Lionel-Lim/data-marble-machine/log/pics/partDesign.jpeg

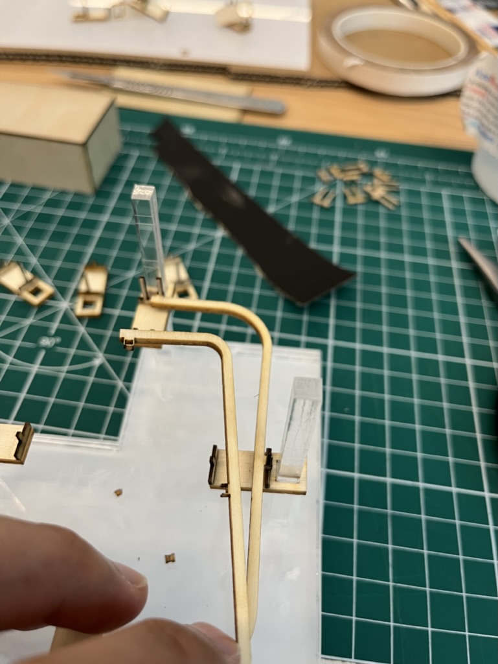
log/pics/partDesign.jpeg
