Lionel-Lim/data-marble-machine/log/pics/wheelWoodMat.jpeg

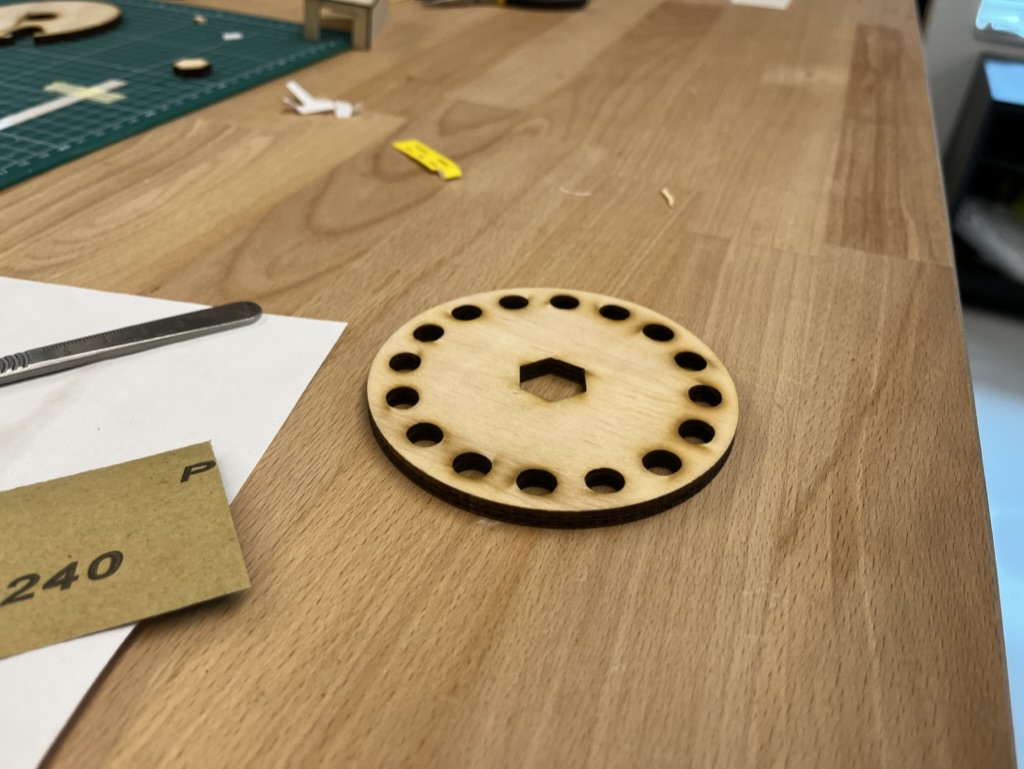
log/pics/wheelWoodMat.jpeg
