Lionel-Lim/data-marble-machine/report/resource/copper lane.png

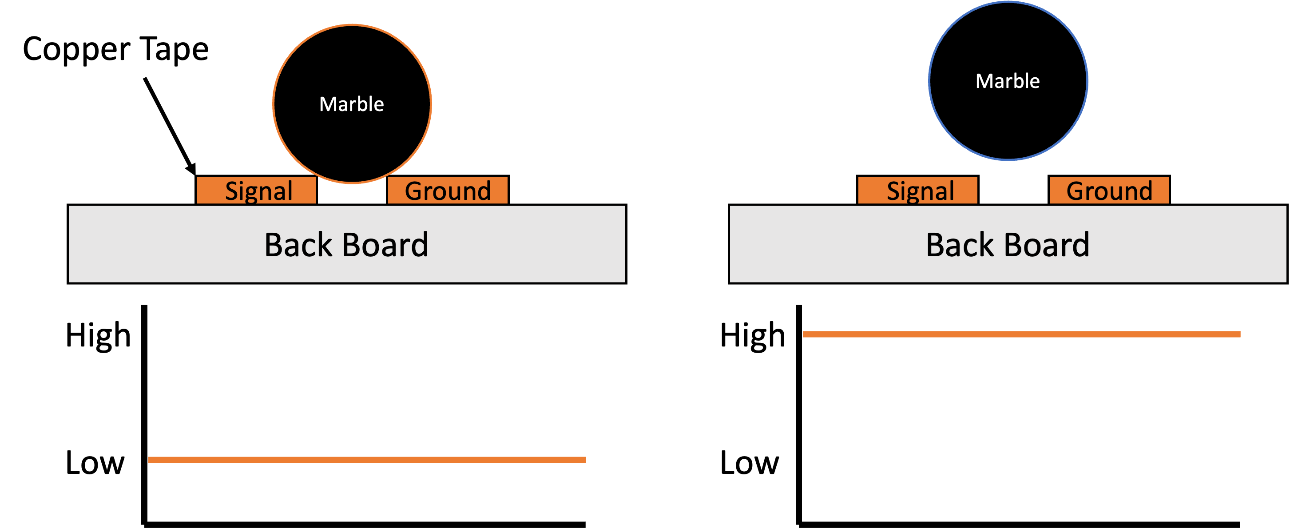
report/resource/copper lane.png
