Lionel-Lim/data-marble-machine/report/resource/device logic.png

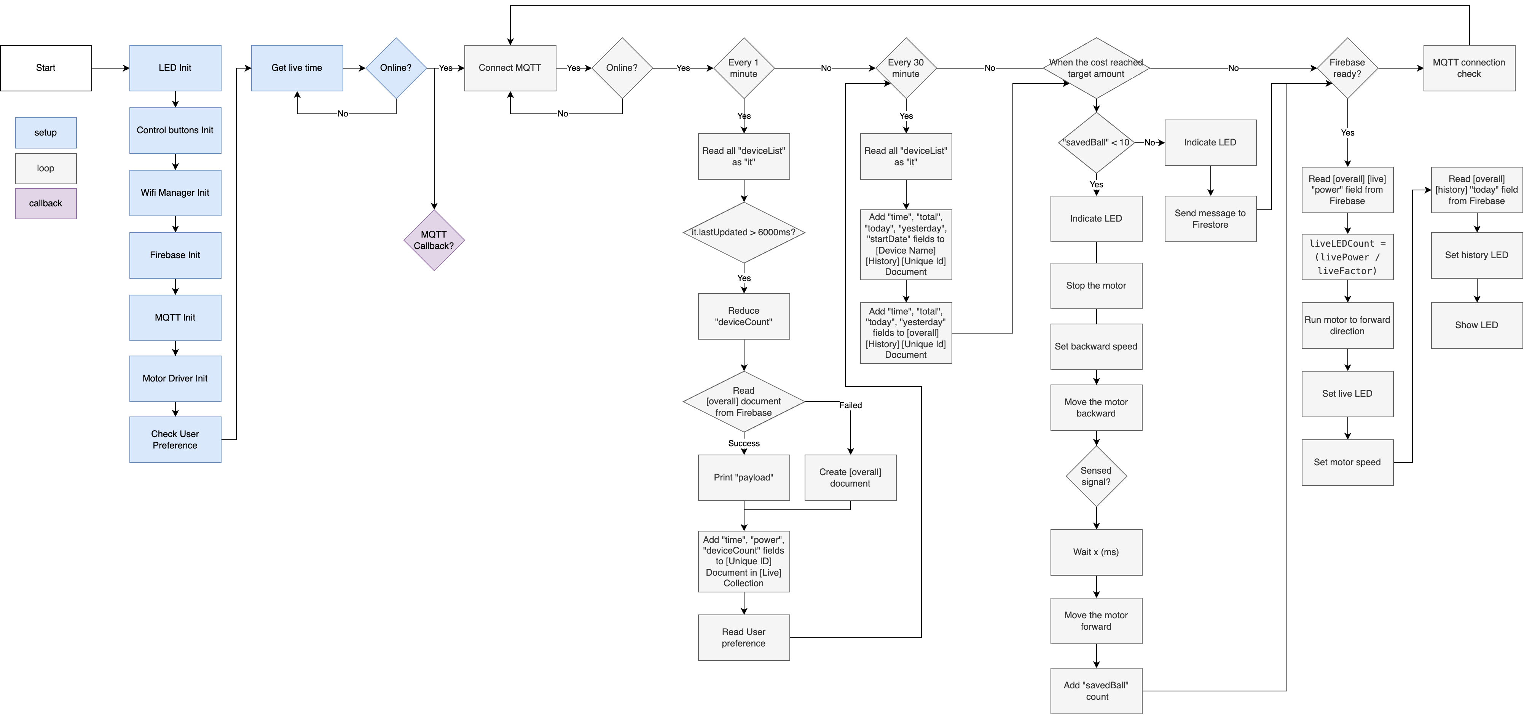
report/resource/device logic.png
