Lionel-Lim/data-marble-machine/report/resource/prototype.png

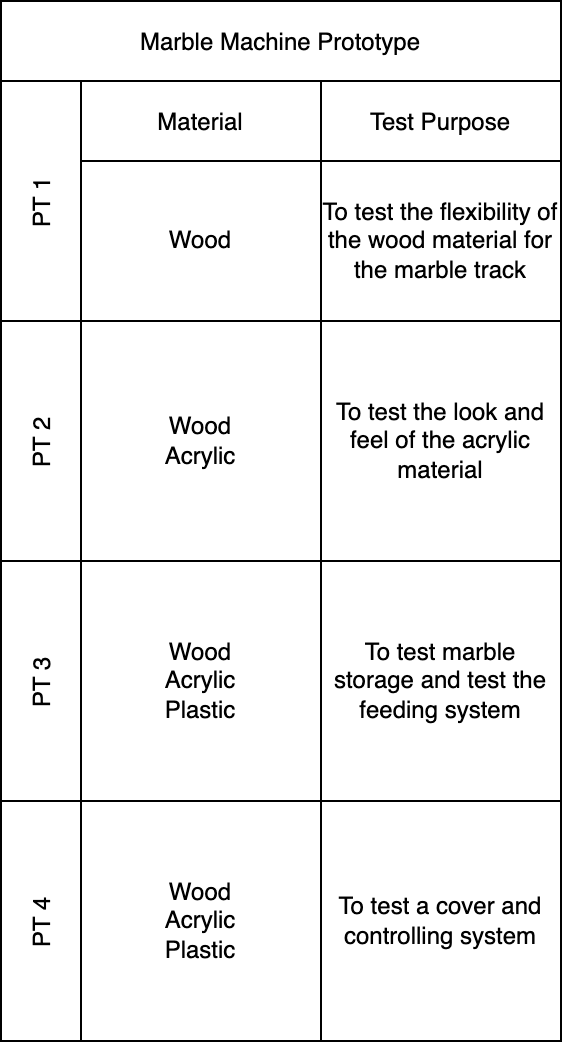
report/resource/prototype.png
