Lionel-Lim/data-marble-machine/report/resource/render.png

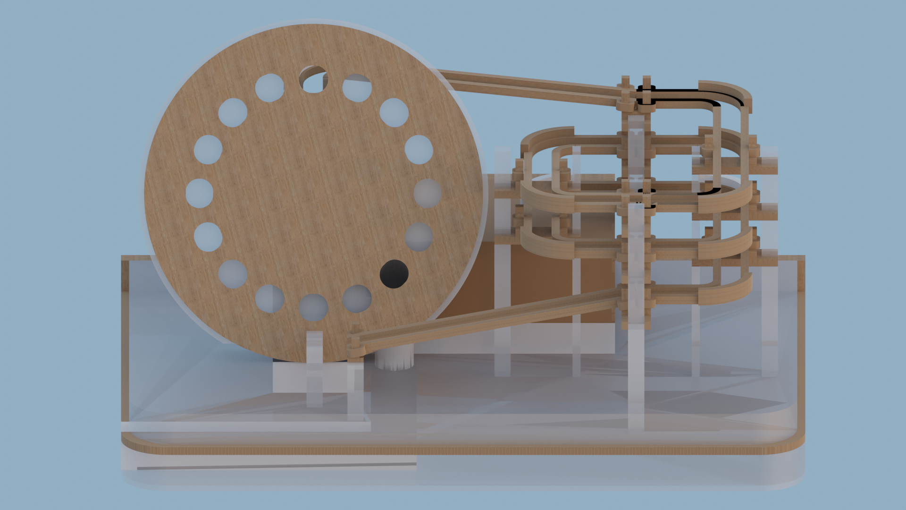
report/resource/render.png
