Lionel-Lim/data-marble-machine/report/resource/track mount.png

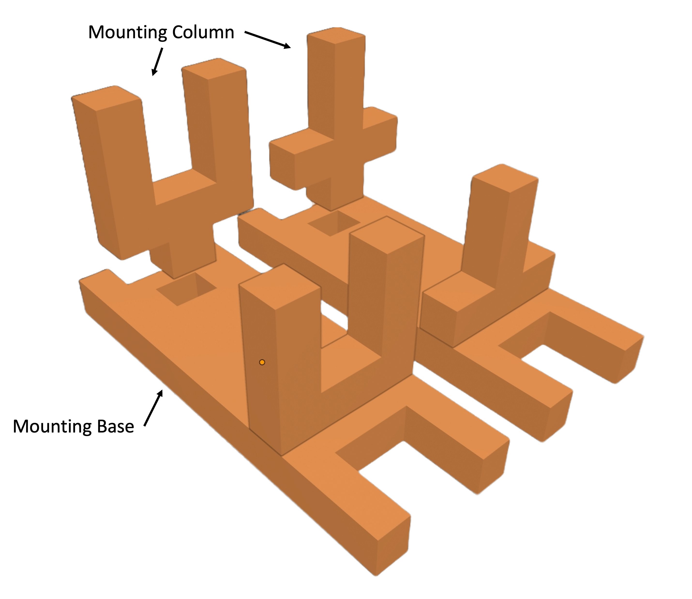
report/resource/track mount.png
