Lionel-Lim/data-marble-machine/models/work in progress/drawings/rev7_NewType/ref_Base.dxf

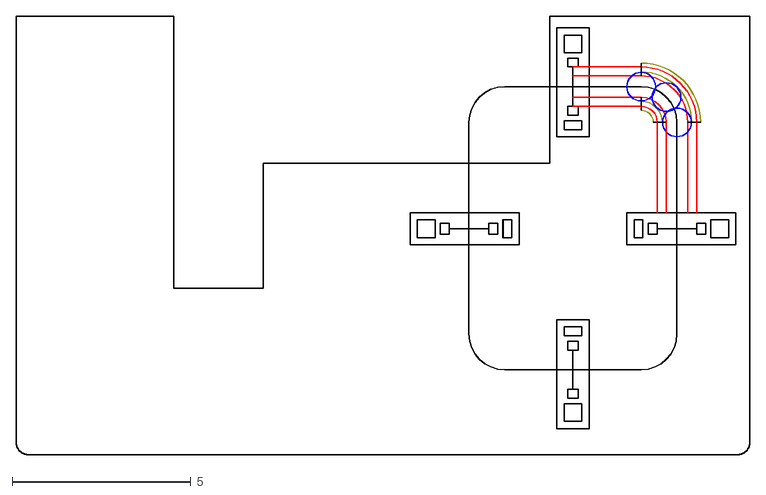
[picture p36: CAD file, 2023-08-10]
models/work in progress/drawings/rev7_NewType/ref_Base.dxf
20.5 x 12.2
