Lionel-Lim/data-marble-machine/models/work in progress/drawings/rev9/ent.dxf

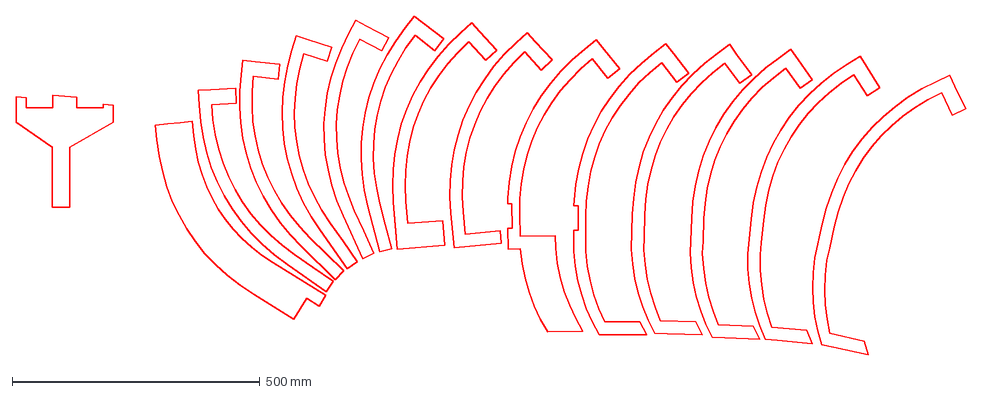
[picture p37: CAD file, 2023-08-10]
models/work in progress/drawings/rev9/ent.dxf
1914.8 x 683.8 mm
