Lionel-Lim/data-marble-machine/models/work in progress/drawings/tracks/track5_page2.dxf

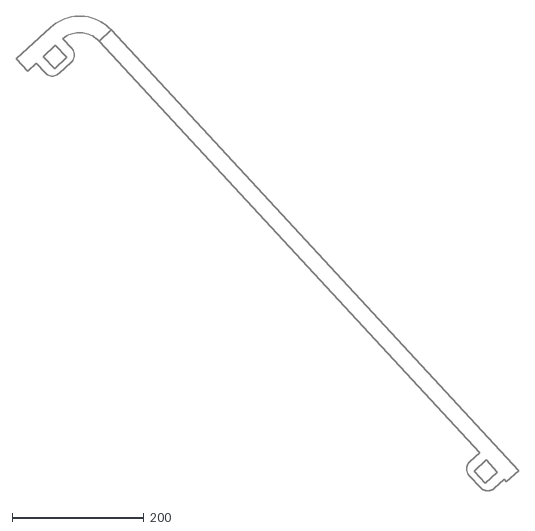
[picture p38: CAD file, 2023-07-11]
models/work in progress/drawings/tracks/track5_page2.dxf
761.8 x 720.3
