Lionel-Lim/data-marble-machine/models/work in progress/3dprint/rev6_newtype/gearBase.stl

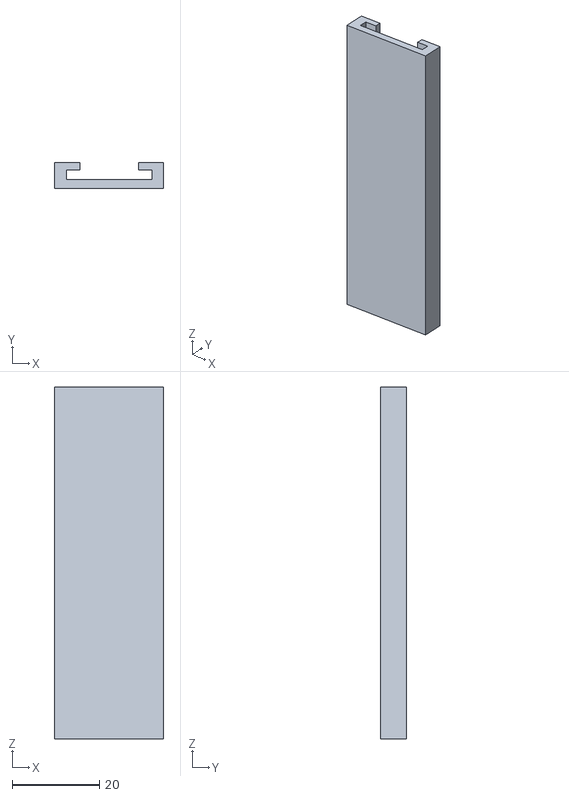
[picture p39: CAD file, 2023-08-10]
models/work in progress/3dprint/rev6_newtype/gearBase.stl
25.0 x 5.90 x 80.8
