Lionel-Lim/data-marble-machine/models/work in progress/3dprint/tube.stl

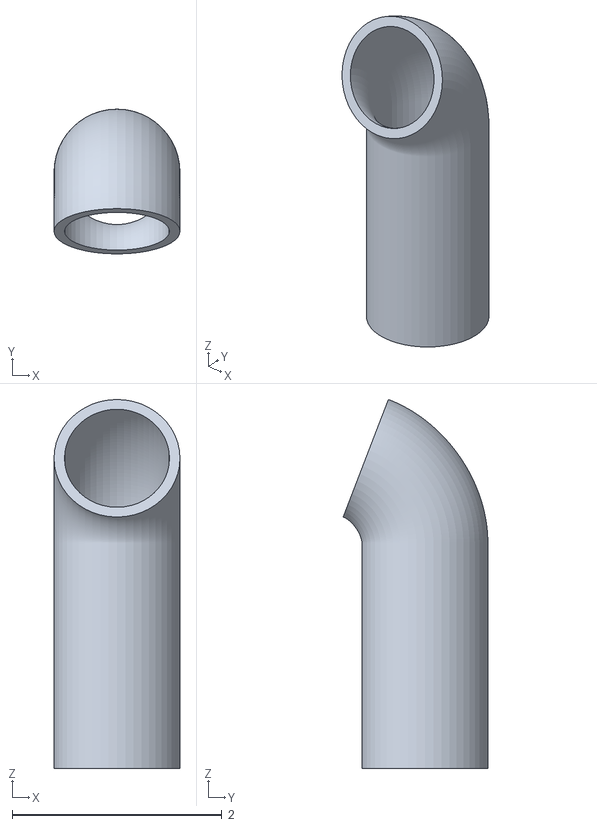
[picture p40: CAD file, 2023-07-11]
models/work in progress/3dprint/tube.stl
1.20 x 1.38 x 3.52
