Lionel-Lim/data-marble-machine/models/work in progress/drawings/final/5mm_acrylic.dxf

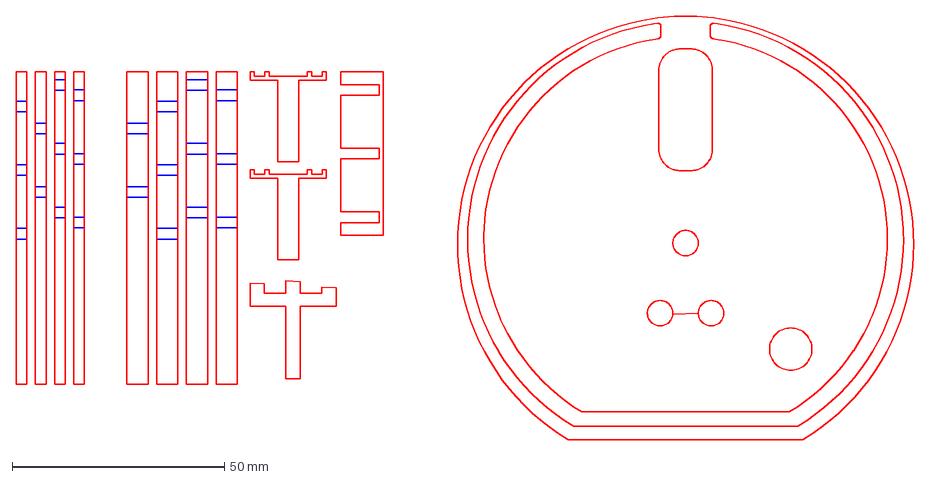
[picture p41: CAD file, 2023-08-10]
models/work in progress/drawings/final/5mm_acrylic.dxf
211.2 x 99.7 mm
