Lionel-Lim/data-marble-machine/models/work in progress/drawings/tracks/track3_page2.dxf

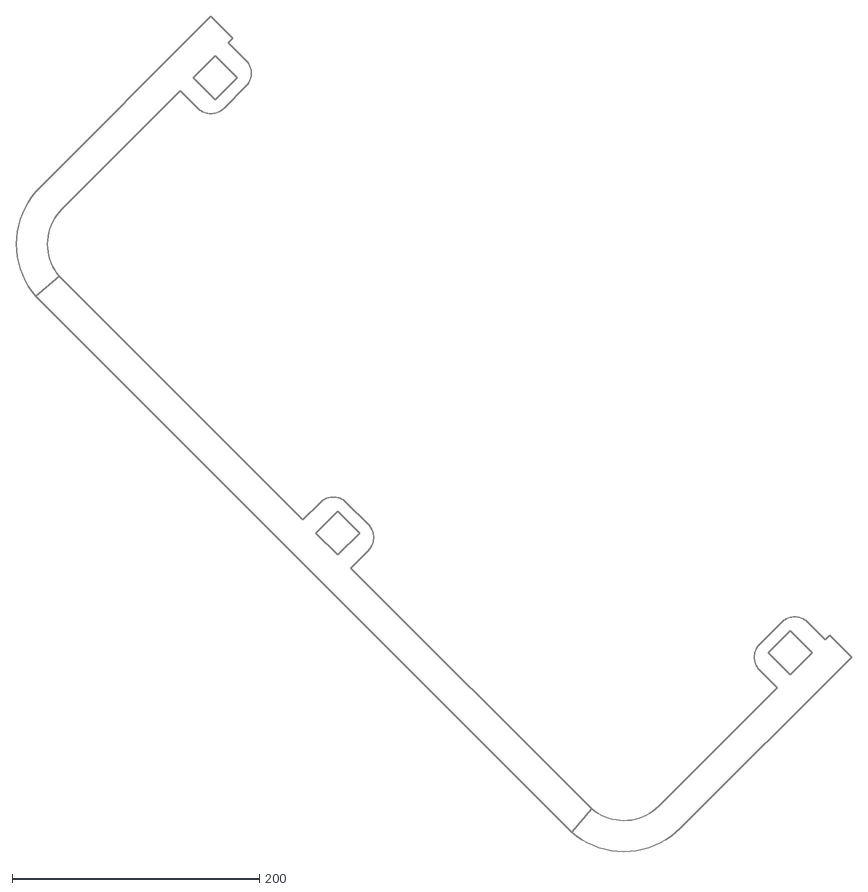
[picture p42: CAD file, 2023-07-11]
models/work in progress/drawings/tracks/track3_page2.dxf
675.7 x 675.7
