Lionel-Lim/data-marble-machine/models/work in progress/3dprint/rev6_newtype/gearTower.stl

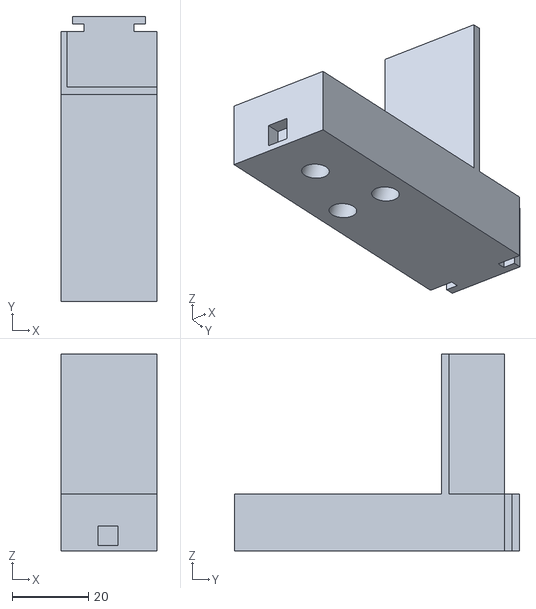
[picture p43: CAD file, 2023-08-10]
models/work in progress/3dprint/rev6_newtype/gearTower.stl
25.1 x 74.9 x 51.7
