Lionel-Lim/data-marble-machine/models/work in progress/3dprint/wheel.stl

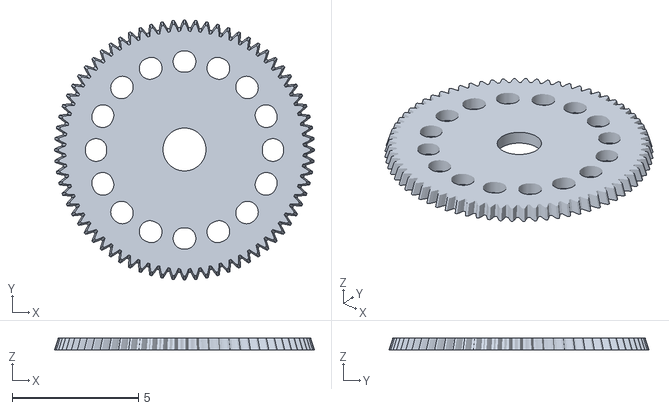
[picture p44: CAD file, 2023-07-11]
models/work in progress/3dprint/wheel.stl
10.3 x 10.3 x 0.478
