Lionel-Lim/data-marble-machine/models/work in progress/drawings/final/control box.dxf

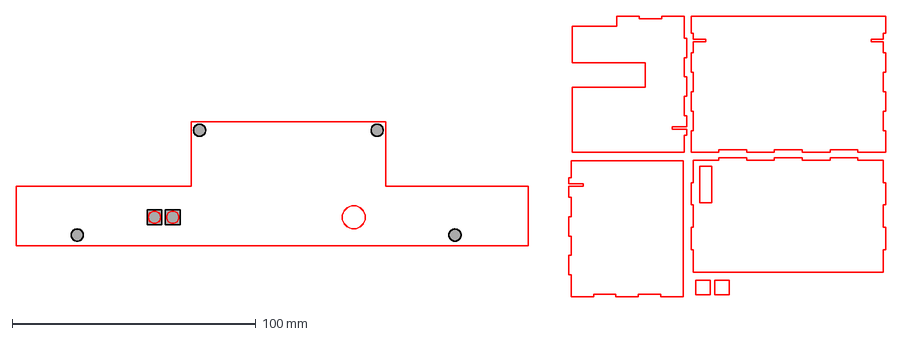
[picture p45: CAD file, 2023-08-10]
models/work in progress/drawings/final/control box.dxf
356.8 x 115.1 mm
