Lionel-Lim/data-marble-machine/models/work in progress/drawings/tracks/track4_page1.dxf

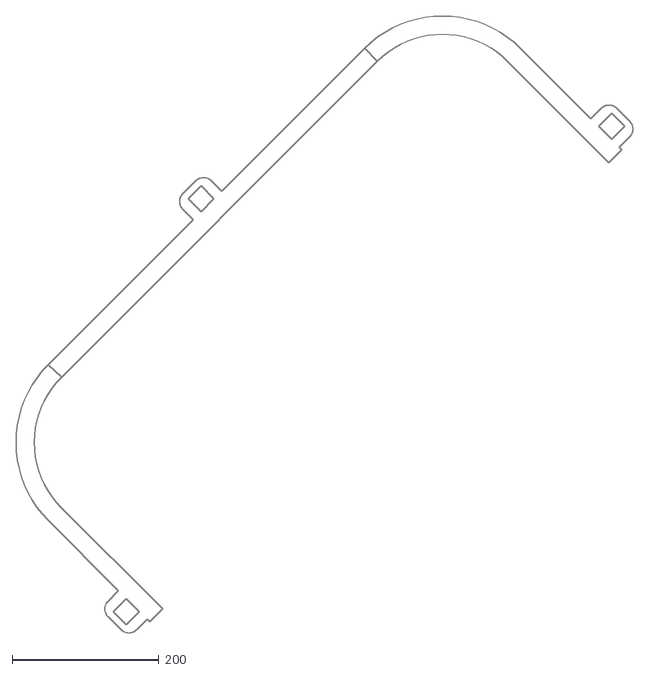
[picture p46: CAD file, 2023-07-11]
models/work in progress/drawings/tracks/track4_page1.dxf
840.3 x 840.3
