Lionel-Lim/data-marble-machine/models/work in progress/3dprint/3dparts.stl

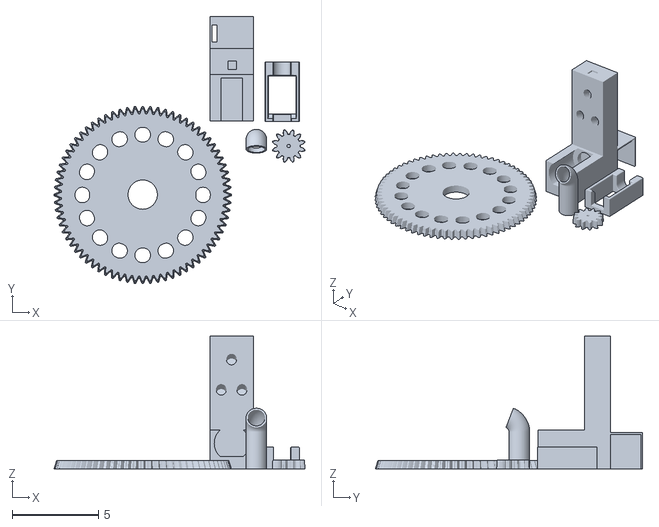
[picture p47: CAD file, 2023-07-11]
models/work in progress/3dprint/3dparts.stl
14.6 x 15.5 x 7.69
