Lionel-Lim/data-marble-machine/models/work in progress/3dprint/rev6_newtype/largeGear.stl

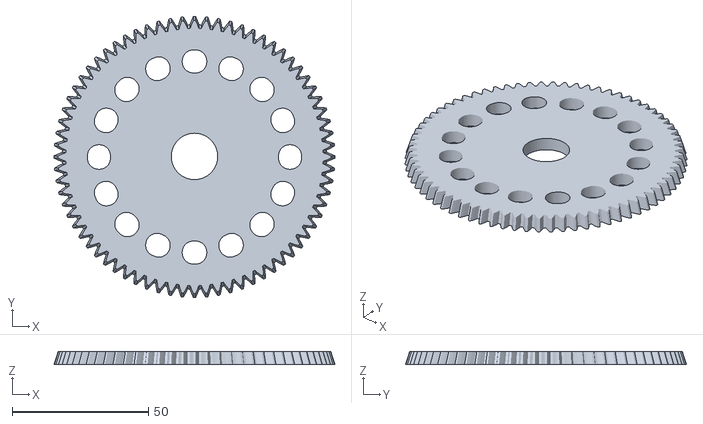
[picture p48: CAD file, 2023-08-10]
models/work in progress/3dprint/rev6_newtype/largeGear.stl
102.9 x 102.9 x 4.78
