Lionel-Lim/data-marble-machine/models/work in progress/drawings/tracks/track4_page2.dxf

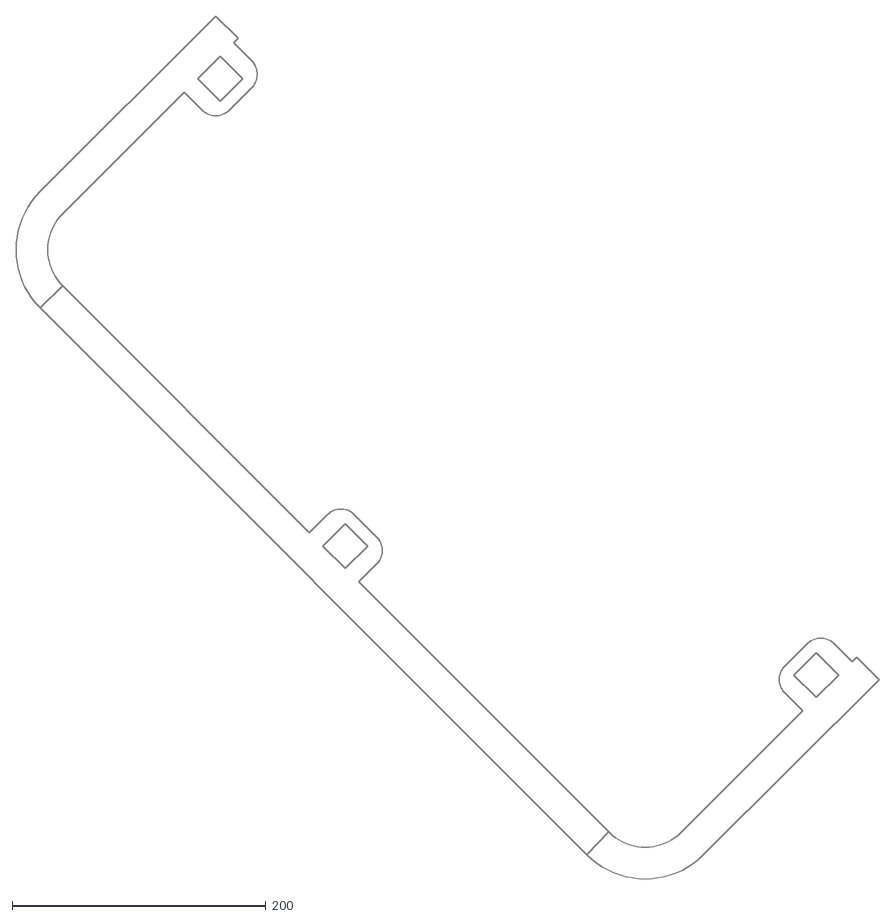
[picture p49: CAD file, 2023-07-11]
models/work in progress/drawings/tracks/track4_page2.dxf
680.1 x 680.1
