Lionel-Lim/data-marble-machine/models/final/3d print/motorBox_base.stl

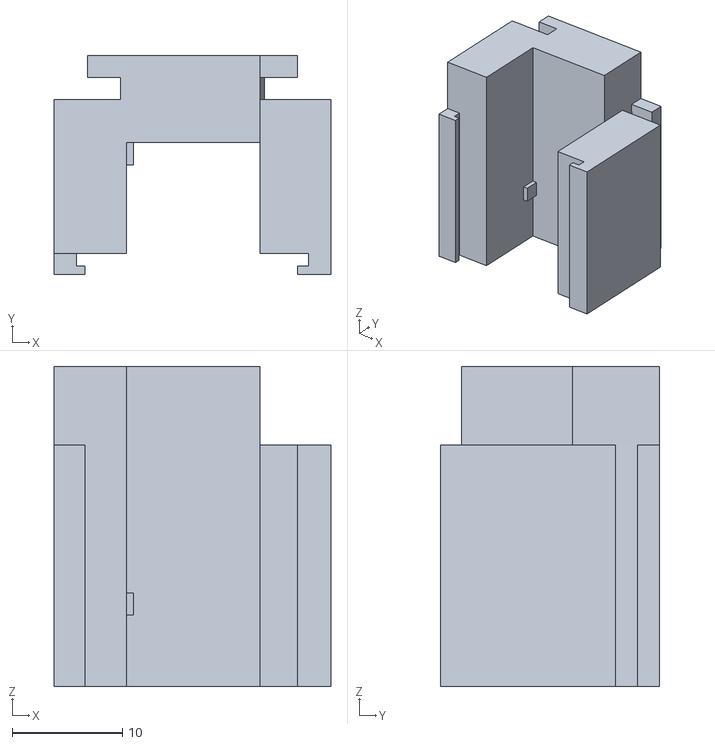
[picture p50: CAD file, 2023-08-10]
models/final/3d print/motorBox_base.stl
25.1 x 19.9 x 29.1
