Lionel-Lim/data-marble-machine/models/work in progress/3dprint/motorHolder.stl

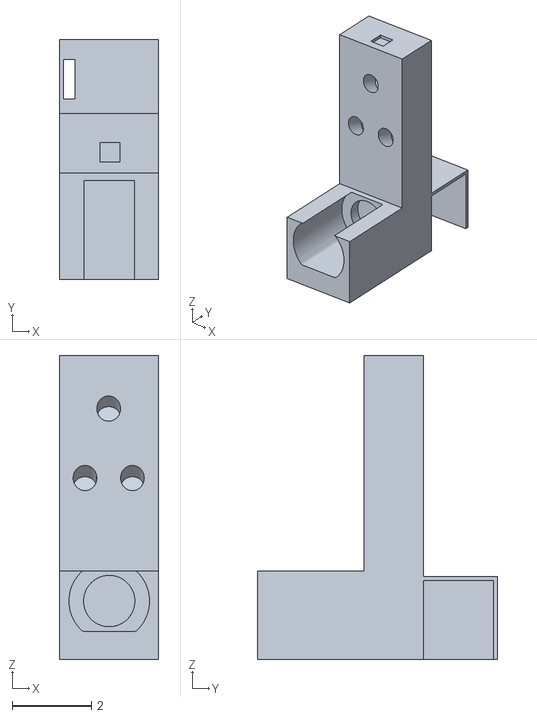
[picture p51: CAD file, 2023-07-11]
models/work in progress/3dprint/motorHolder.stl
2.51 x 6.07 x 7.69
