Lionel-Lim/data-marble-machine/models/work in progress/drawings/final/10mm_acrylic.dxf

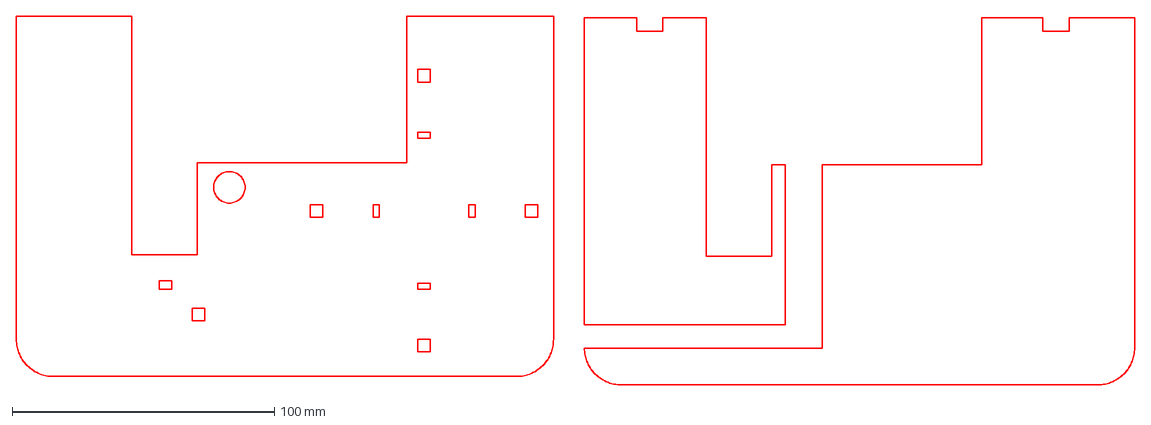
[picture p52: CAD file, 2023-08-10]
models/work in progress/drawings/final/10mm_acrylic.dxf
426.8 x 140.7 mm
