Lionel-Lim/data-marble-machine/models/work in progress/drawings/tracks/track2_page1.dxf

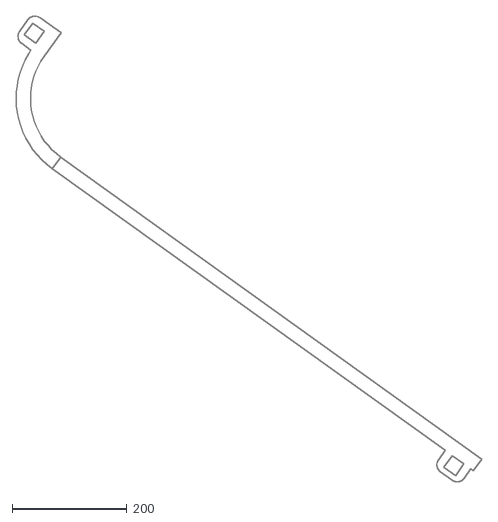
[picture p53: CAD file, 2023-07-11]
models/work in progress/drawings/tracks/track2_page1.dxf
810.3 x 810.3
