Lionel-Lim/data-marble-machine/models/work in progress/3dprint/rev6_newtype/device_base.stl

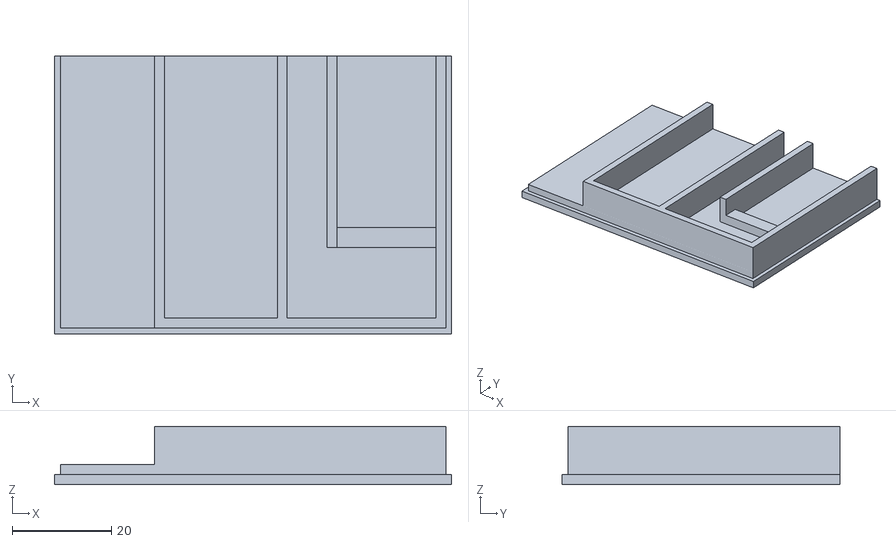
[picture p54: CAD file, 2023-08-10]
models/work in progress/3dprint/rev6_newtype/device_base.stl
80.0 x 56.0 x 11.7
