Lionel-Lim/data-marble-machine/models/work in progress/3dprint/subGear.stl

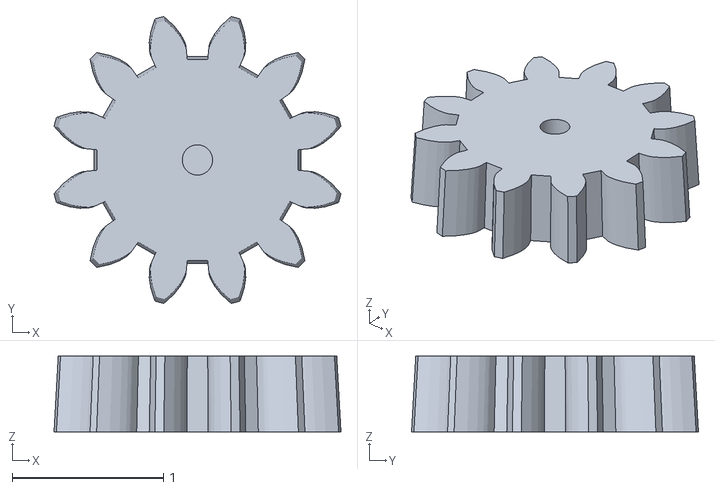
[picture p55: CAD file, 2023-07-11]
models/work in progress/3dprint/subGear.stl
1.90 x 1.90 x 0.499
