Lionel-Lim/data-marble-machine/models/work in progress/drawings/rev7_NewType/5mm_wood.dxf

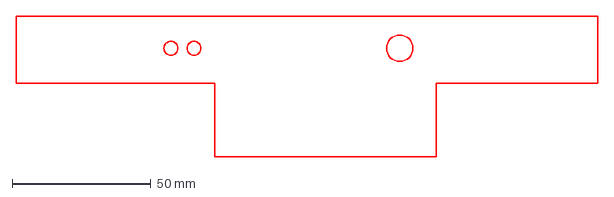
[picture p56: CAD file, 2023-08-10]
models/work in progress/drawings/rev7_NewType/5mm_wood.dxf
210.0 x 50.8 mm
