Lionel-Lim/data-marble-machine/models/work in progress/drawings/tracks/track1.dxf

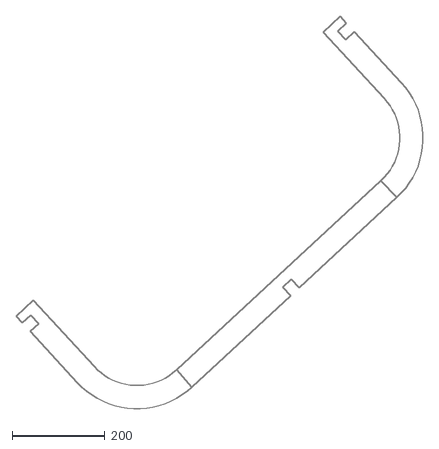
[picture p57: CAD file, 2023-07-11]
models/work in progress/drawings/tracks/track1.dxf
878.9 x 846.7
