Lionel-Lim/data-marble-machine/models/work in progress/3dprint/gearPinion.stl

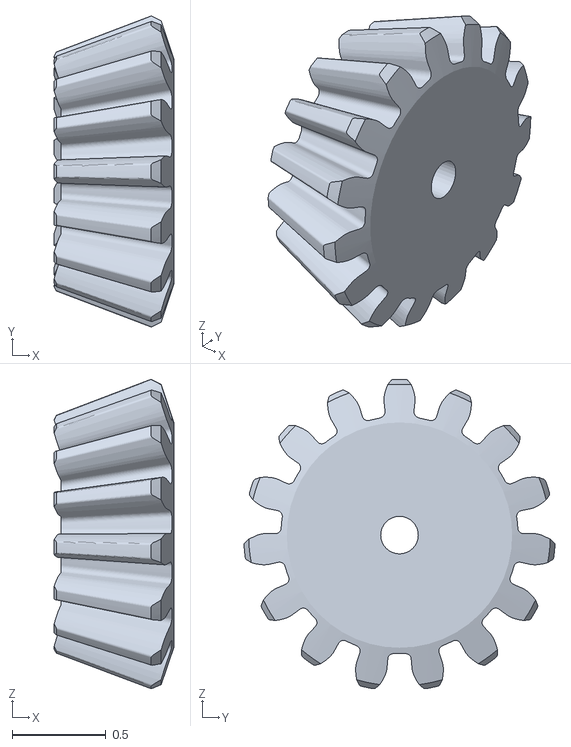
[picture p58: CAD file, 2023-06-22]
models/work in progress/3dprint/gearPinion.stl
0.637 x 1.66 x 1.65
