Lionel-Lim/data-marble-machine/models/work in progress/3dprint/rev6_newtype/motorBox_top.stl

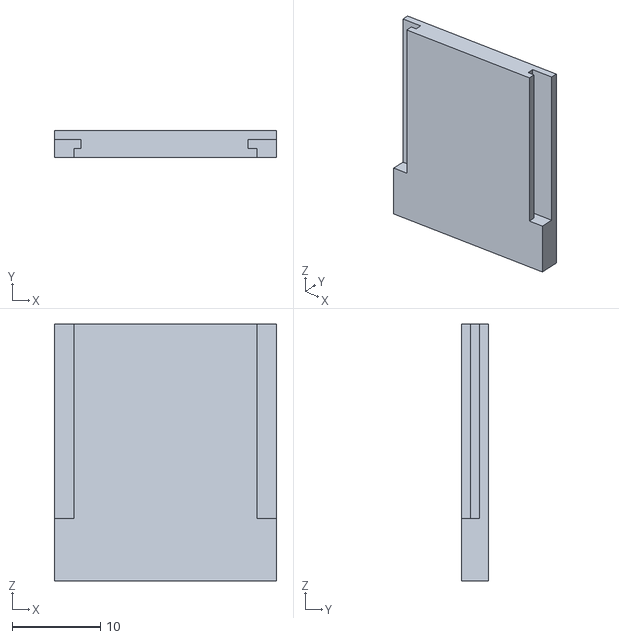
[picture p59: CAD file, 2023-08-10]
models/work in progress/3dprint/rev6_newtype/motorBox_top.stl
25.1 x 3.00 x 29.1
