Lionel-Lim/data-marble-machine/models/work in progress/drawings/tracks/track2_page2.dxf

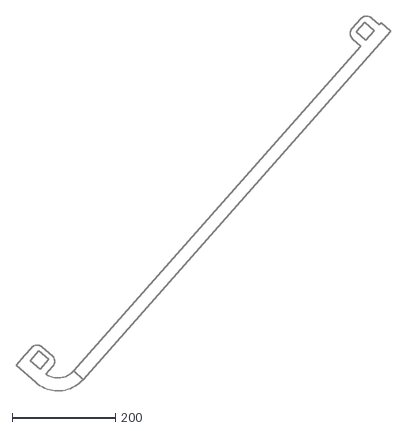
[picture p60: CAD file, 2023-07-11]
models/work in progress/drawings/tracks/track2_page2.dxf
727.4 x 727.4
