Lionel-Lim/data-marble-machine/models/work in progress/3dprint/gearGear.stl

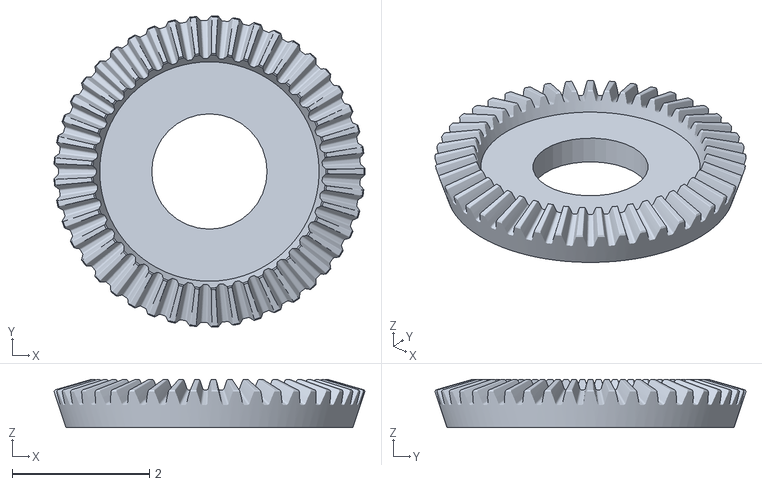
[picture p61: CAD file, 2023-06-22]
models/work in progress/3dprint/gearGear.stl
4.54 x 4.54 x 0.705
