Lionel-Lim/data-marble-machine/models/work in progress/drawings/tracks/track3_page1.dxf

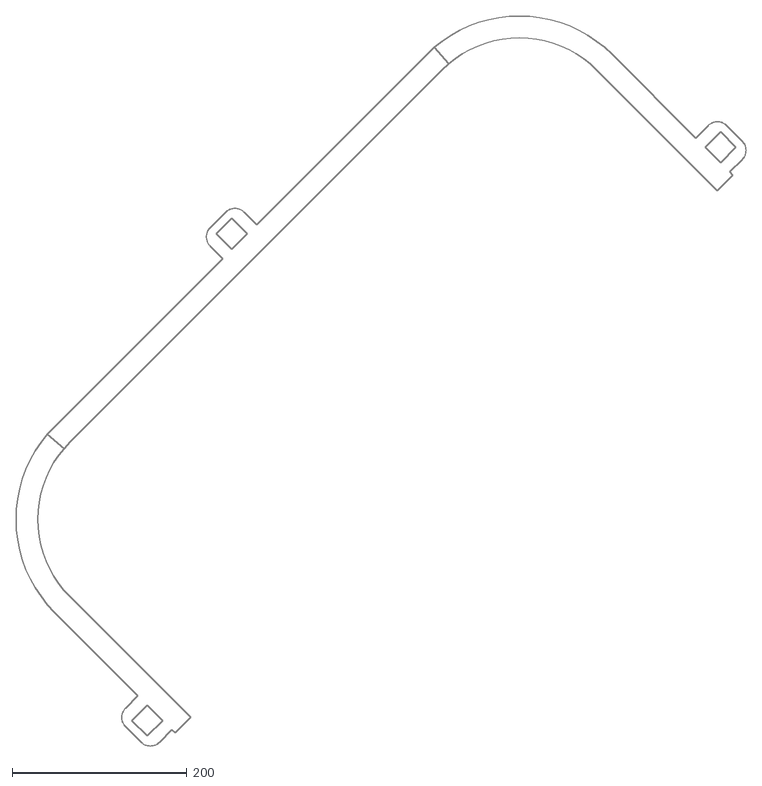
[picture p62: CAD file, 2023-07-11]
models/work in progress/drawings/tracks/track3_page1.dxf
835.9 x 835.9
