Lionel-Lim/data-marble-machine/models/work in progress/3dprint/parts.stl

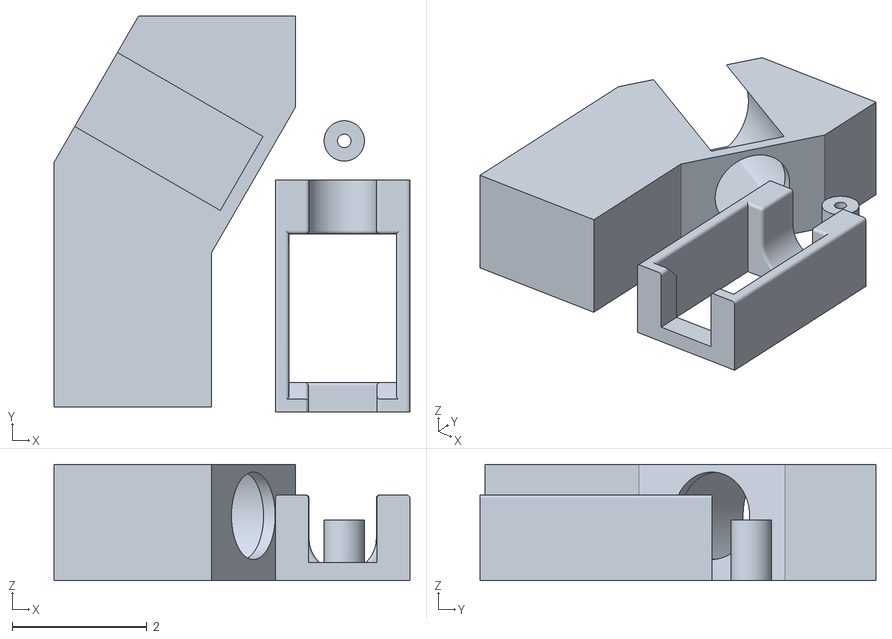
[picture p63: CAD file, 2023-06-22]
models/work in progress/3dprint/parts.stl
5.29 x 5.89 x 1.73
