Lionel-Lim/data-marble-machine/log/pics/figerPrint.jpeg

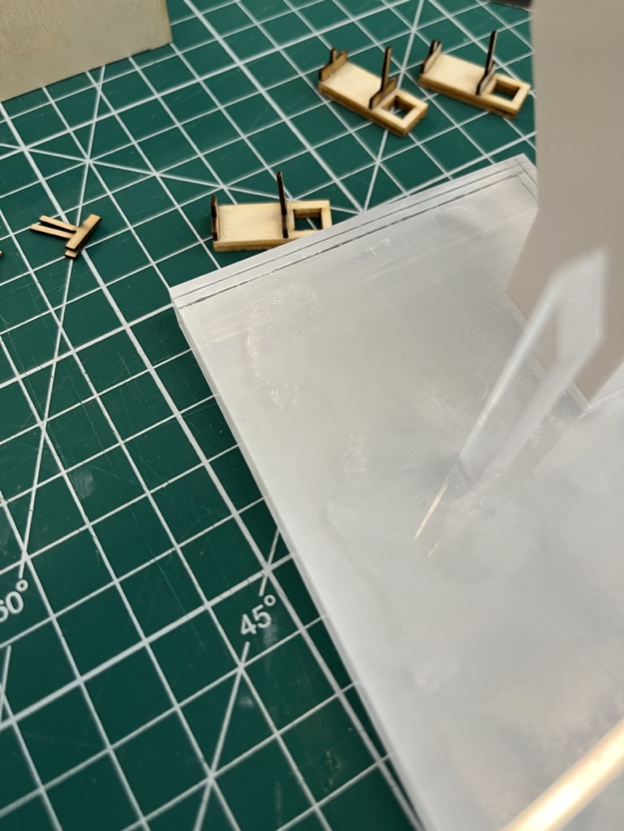
log/pics/figerPrint.jpeg
