Lionel-Lim/data-marble-machine/log/pics/easyFabTest.jpeg

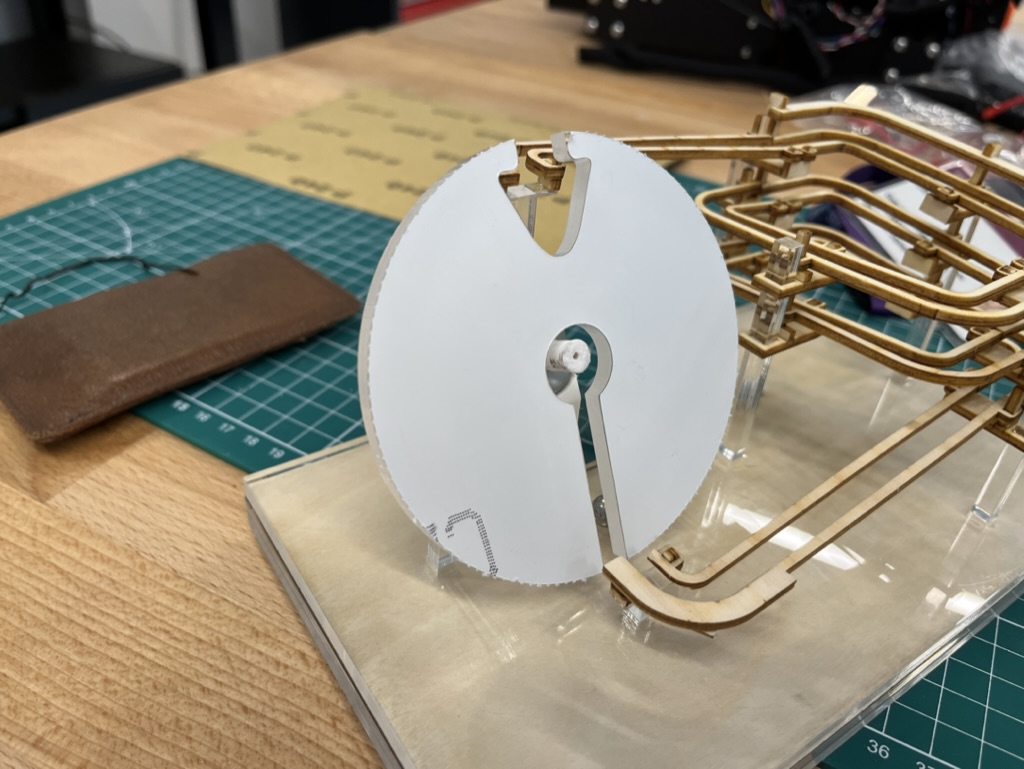
log/pics/easyFabTest.jpeg
