Lionel-Lim/data-marble-machine/log/pics/motorTest.jpeg

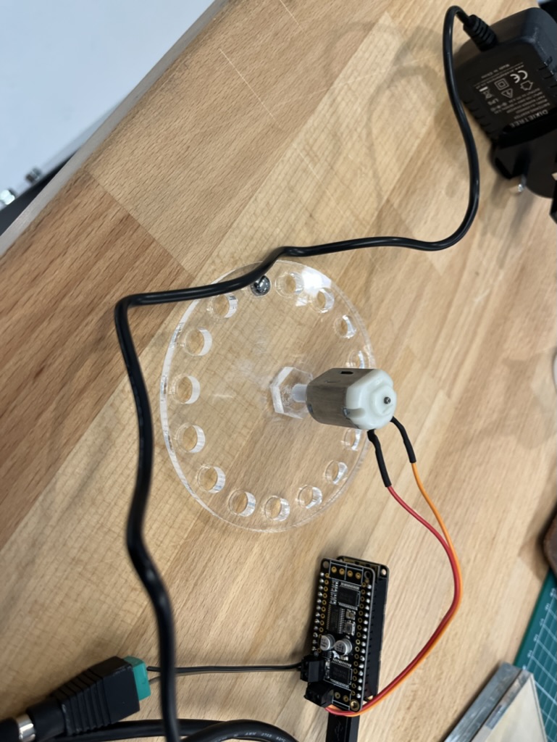
log/pics/motorTest.jpeg
